OPRobots/UltiBot/source_code/STM32F4CCU6/include/menu.h

#ifndef __MENU_H
#define __MENU_H

#include "leds.h"
#include "control.h"
#include "debug.h"

#define NUM_MENUS 4
enum MENUS {
  MENU_NONE = 0,
  MENU_OPENING = 1,
  MENU_STRAT = 2,
  MENU_DEBUG = 3
};

void check_menu_button(void);
void menu_mode_change(void);
void menu_config_change(void);

#endif
