OPRobots/UltiBot/source_code/STM32F4CCU6/include/setup.h

#ifndef __SETUP_H
#define __SETUP_H

#include <libopencm3/cm3/dwt.h>
#include <libopencm3/cm3/nvic.h>
#include <libopencm3/cm3/systick.h>
#include <libopencm3/stm32/adc.h>
#include <libopencm3/stm32/dma.h>
#include <libopencm3/stm32/exti.h>
#include <libopencm3/stm32/gpio.h>
#include <libopencm3/stm32/rcc.h>
#include <libopencm3/stm32/timer.h>
#include <libopencm3/stm32/usart.h>

#include <stdio.h>
#include <stdlib.h>
#include <string.h>

#include "command.h"
#include "config.h"
#include "leds.h"
#include "sensors.h"
#include "rc5.h"

void setup(void);

#endif
